Taolink-Tech/TK8620-ELRS/tools/burn/bootpatch.h

#ifndef BOOTPATCH_H
#define BOOTPATCH_H
#include <iostream>

#define OPCODE_VERSION_GET          0x00
#define OPCODE_VERSION_GET_ACK      0x01
#define OPCODE_WRITE                0x02
#define OPCODE_WRITE_ACK            0x03
#define OPCODE_WRITE_RAM            0x04
#define OPCODE_WRITE_RAM_ACK        0x05
#define OPCODE_READ                 0x08
#define OPCODE_READ_ACK             0x09
#define OPCODE_ERASE                0x0C
#define OPCODE_ERASE_ACK            0x0D
#define OPCODE_DISCONNECT           0x10
#define OPCODE_DISCONNECT_ACK       0x11
#define OPCODE_CHANGE_BAUDRATE      0x12
#define OPCODE_CHANGE_BAUDRATE_ACK  0x13
#define OPCODE_EXECUTE_CODE         0x15
#define OPCODE_EXECUTE_CODE_END     0x17
#define OPCODE_CALC_CRC32           0x19
#define OPCODE_CALC_CRC32_ACK       0x1a
#define OPCODE_UNLOCK_FLASH         0x1f
#define OPCODE_UNLOCK_FLASH_ACK     0x20
#define OPCODE_LOCK_FLASH           0x21
#define OPCODE_LOCK_FLASH_ACK       0x22
#define OPCODE_BLOCK32K_ERASE       0x1b
#define OPCODE_BLOCK32K_ERASE_ACK   0x1c
#define OPCODE_BLOCK64K_ERASE		0x1d
#define OPCODE_BLOCK64K_ERASE_ACK 	0x1e

struct bootParamStrcut
{
    uint8_t code;
    uint32_t address;
    uint16_t length;
}__attribute__((gcc_struct, packed));

const unsigned int boot_patch_code[] = {
    0xDFF82317,
    0x8AE302E7,
    0x77971101,
    0x87930000,
    0x4394FFA7,
    0x9B794298,
    0x4390C298,
    0x06B74218,
    0x16FDFF88,
    0xC2188F75,
    0x4B1C4398,
    0xE7939B85,
    0xCB1C0047,
    0xE793431C,
    0xC31C0017,
    0x200017B7,
    0x8023475D,
    0x071300E7,
    0x80A30370,
    0x812300E7,
    0x071300E7,
    0x81A305A0,
    0x822300E7,
    0x071300E7,
    0x82A3F960,
    0x071300E7,
    0x83230690,
    0x459D00E7,
    0x20001537,
    0x1B9721F5,
    0x8B930000,
    0x0A379C2B,
    0x1A7D0100,
    0x81818D93,
    0x00007B17,
    0xF7CB0B13,
    0x27B7AC7D,
    0xC7832000,
    0x47210007,
    0x32E78563,
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
};



const unsigned int patch_8620[] = {
    0x0CC0006F,
    0x200807AE,
    0x200807AE,
    0x00000000,
    0x200807AE,
    0x200807AE,
    0x200807AE,
    0x00000000,
    0x200807AE,
    0x200807AE,
    0x200807AE,
    0x200807AE,
    0x200807AE,
    0x200807AE,
    0x200807AE,
    0x200807AE,
    0x200807AE,
    0x00000000,
    0x00000000,
    0x00000000,
    0x00000000,
    0x00000000,
    0x00000000,
    0x00000000,
    0x00000000,
    0x00000000,
    0x00000000,
    0x00000000,
    0x00000000,
    0x00000000,
    0x20080A98,
    0x00000000,
    0x00000000,
    0x00000000,
    0x00000000,
    0x00000000,
    0x00000000,
    0x00000000,
    0x00000000,
    0x00000000,
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
};

bootParamStrcut getBootParam(const uint8_t &code, const uint32_t &address, const uint16_t &length);

#endif // BOOTPATCH_H
